marcusfia/JEMA_CSAQS/wiki/images/active_inactive_sensors.jpg

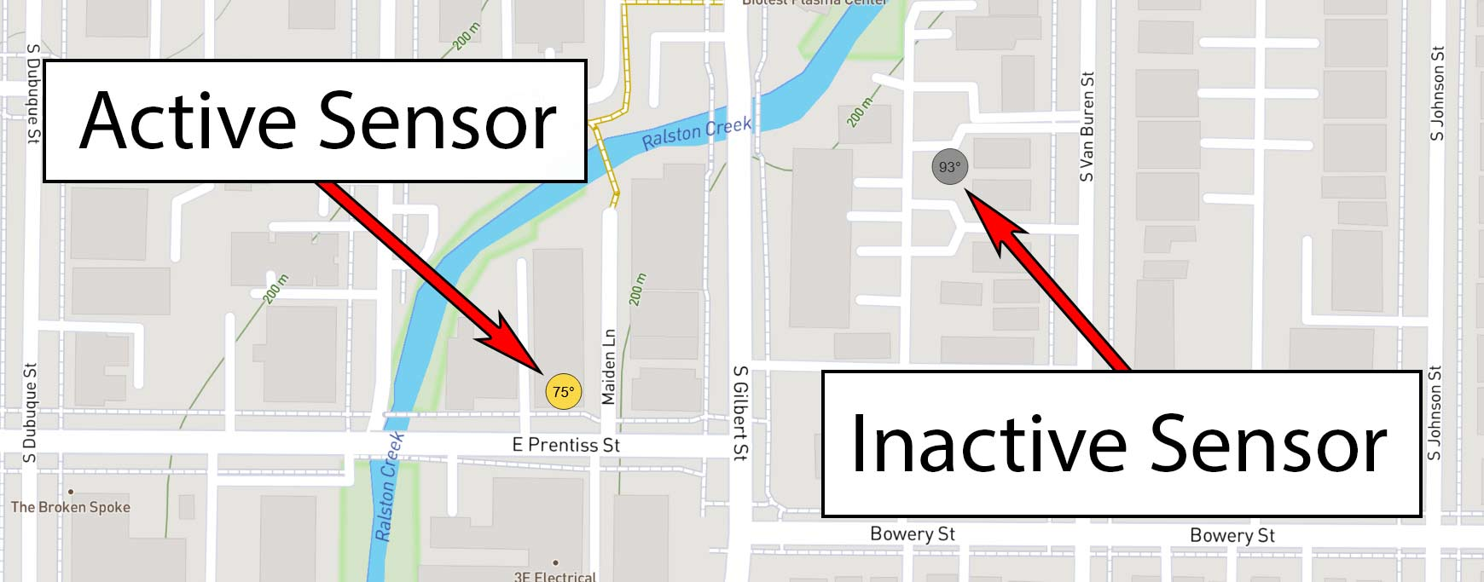
wiki/images/active_inactive_sensors.jpg
