marcusfia/JEMA_CSAQS/wiki/images/antenna.jpg

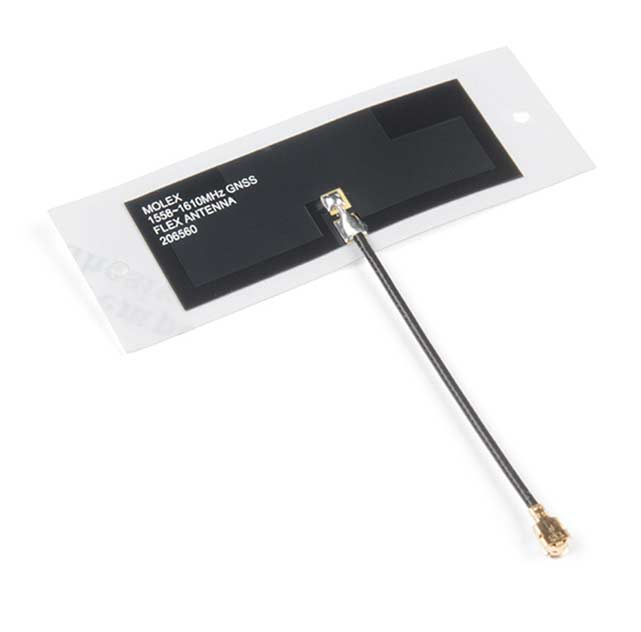
wiki/images/antenna.jpg
