marcusfia/JEMA_CSAQS/wiki/images/batt.jpg

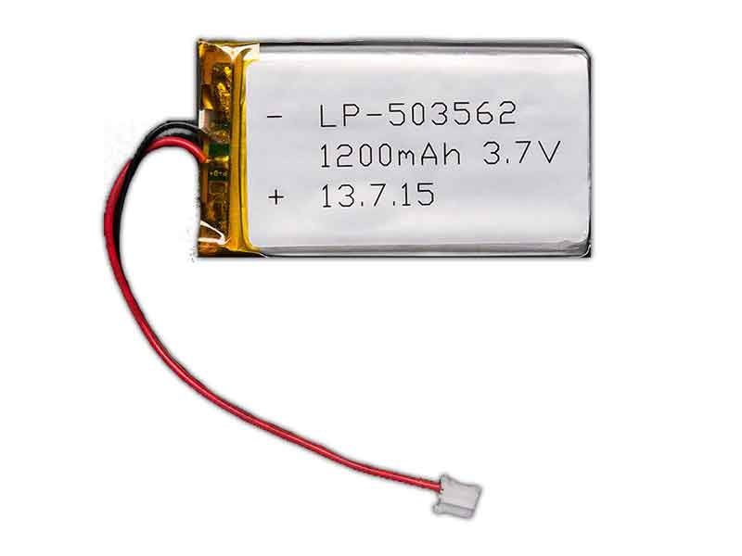
wiki/images/batt.jpg
