marcusfia/JEMA_CSAQS/wiki/images/BME680.jpg

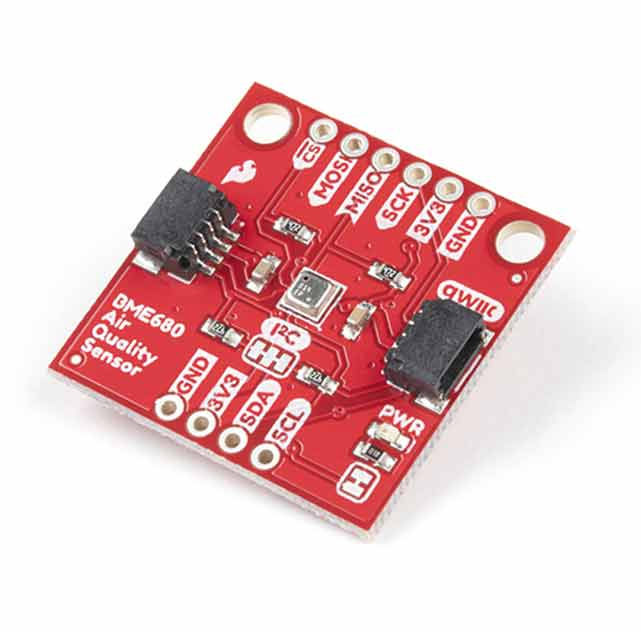
wiki/images/BME680.jpg
