marcusfia/JEMA_CSAQS/wiki/images/cert_3.png

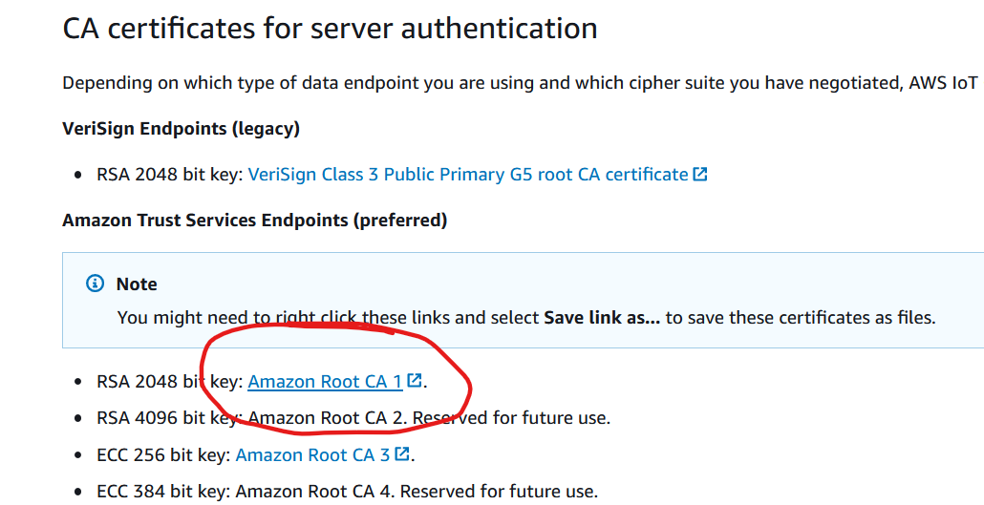
wiki/images/cert_3.png
