marcusfia/JEMA_CSAQS/wiki/images/cert_5.png

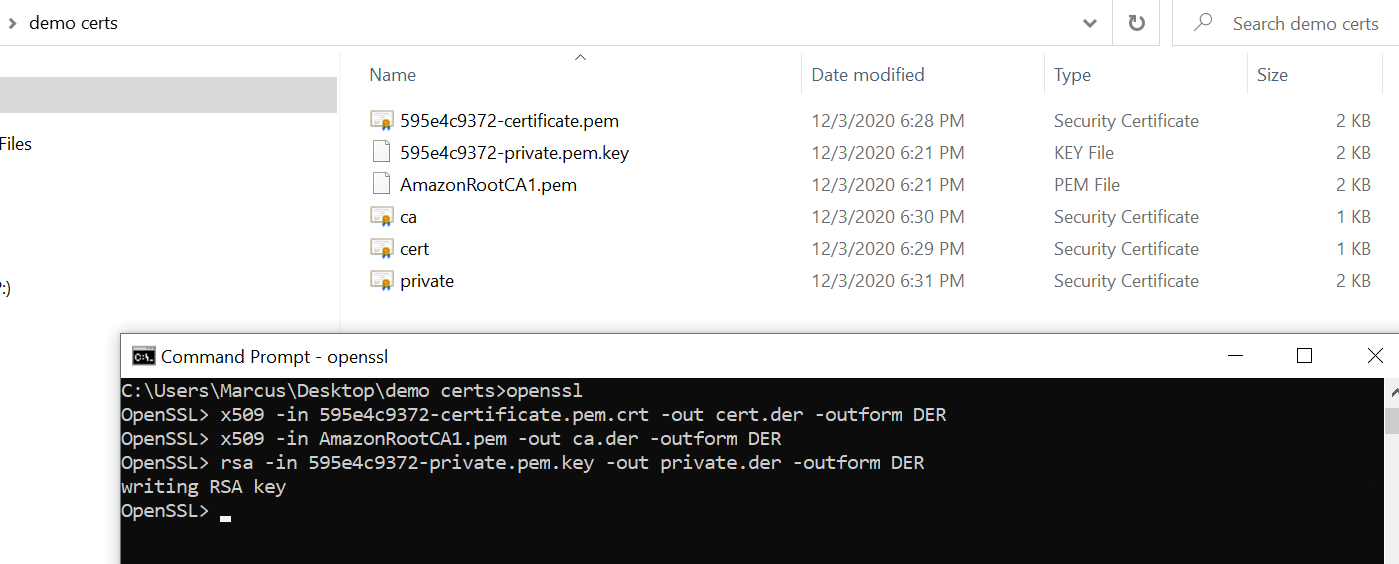
wiki/images/cert_5.png
