marcusfia/JEMA_CSAQS/wiki/images/cert_7.png

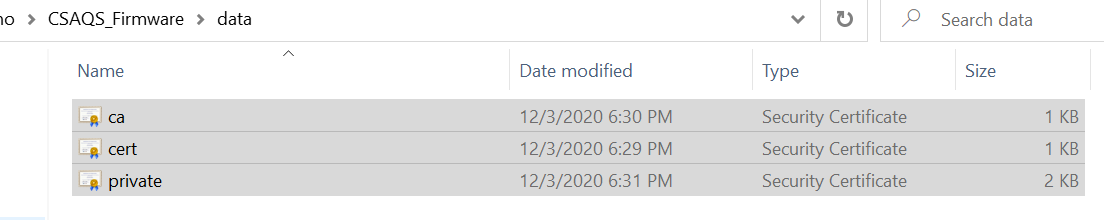
wiki/images/cert_7.png
