marcusfia/JEMA_CSAQS/wiki/images/dataupload.png

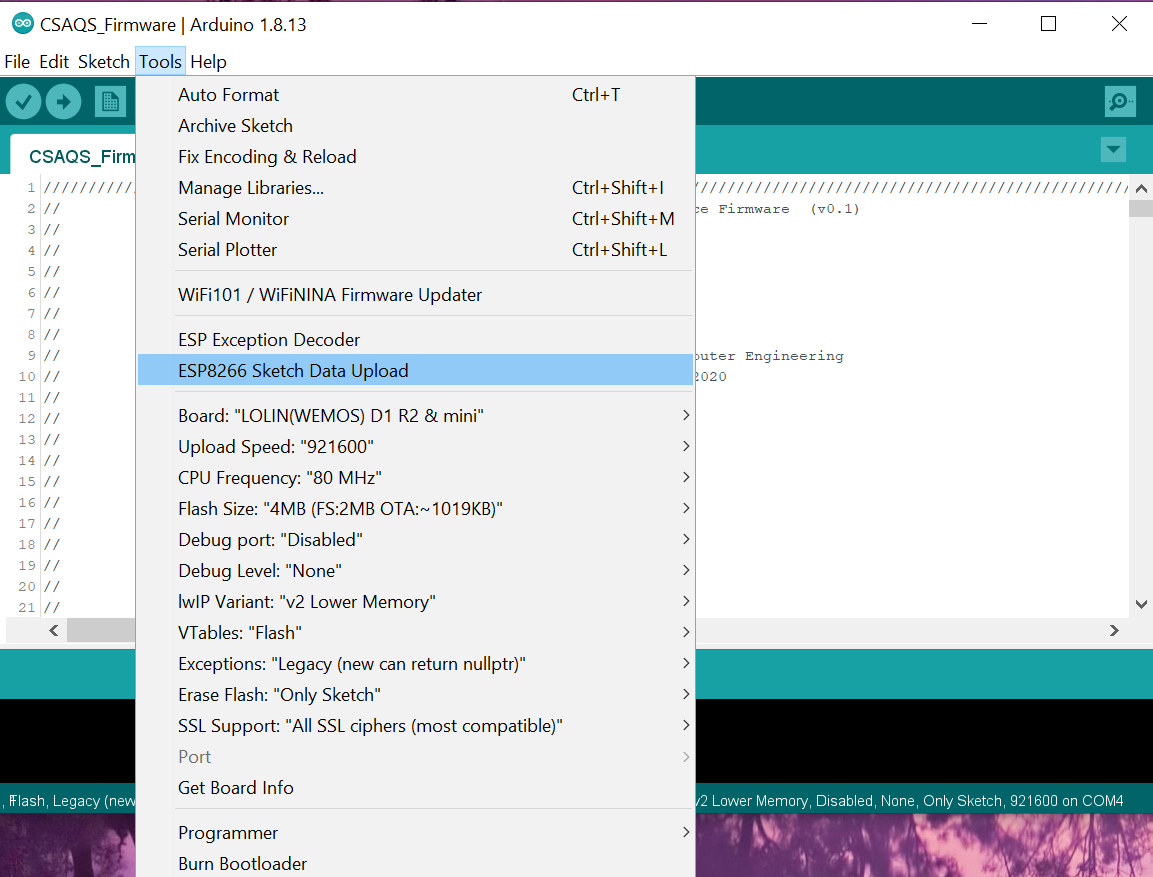
wiki/images/dataupload.png
