marcusfia/JEMA_CSAQS/wiki/images/max30105.jpg

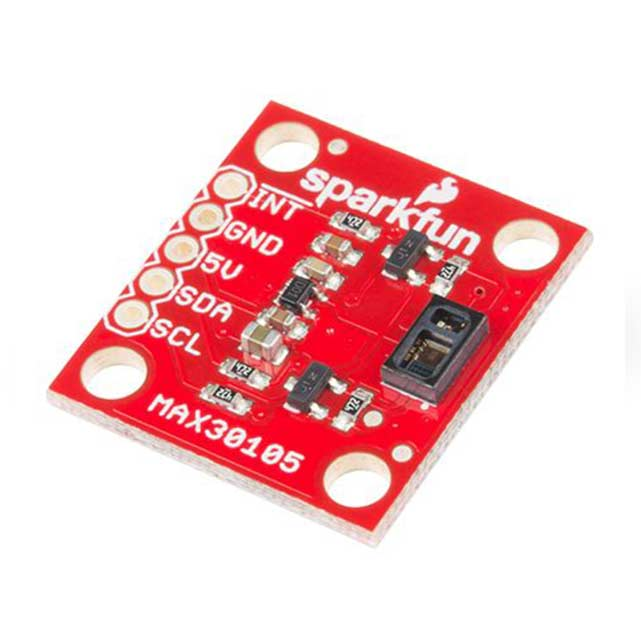
wiki/images/max30105.jpg
