marcusfia/JEMA_CSAQS/wiki/images/mics.jpg

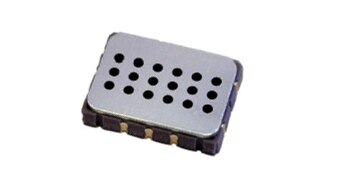
wiki/images/mics.jpg
