marcusfia/JEMA_CSAQS/wiki/images/mobile.jpg

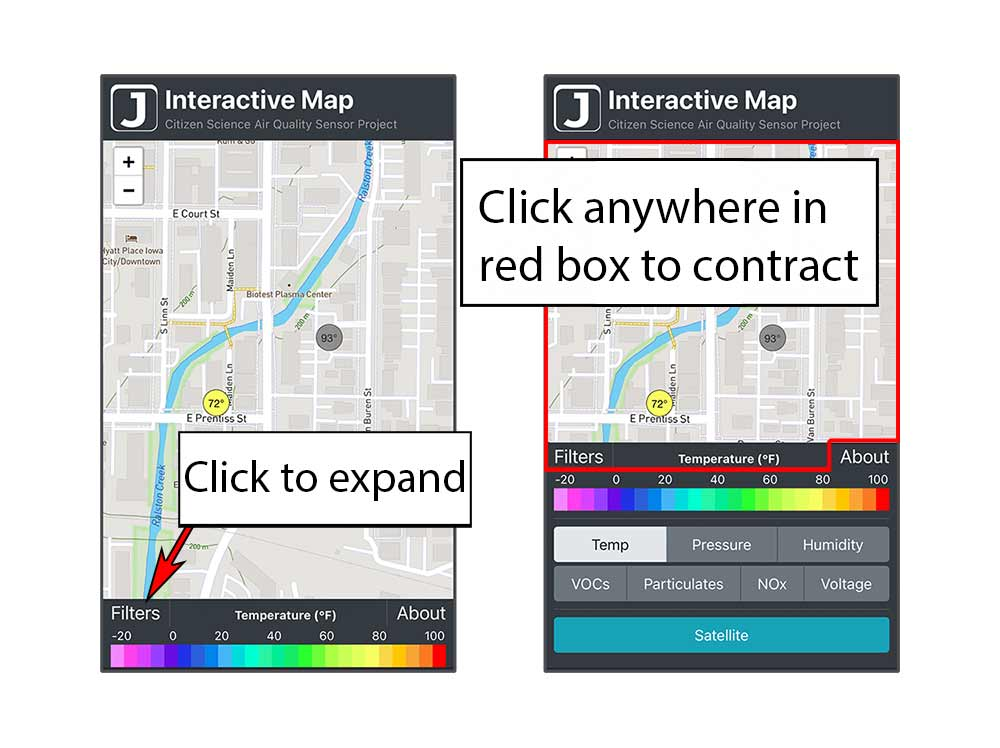
wiki/images/mobile.jpg
