marcusfia/JEMA_CSAQS/wiki/images/NEO-M8U.jpg

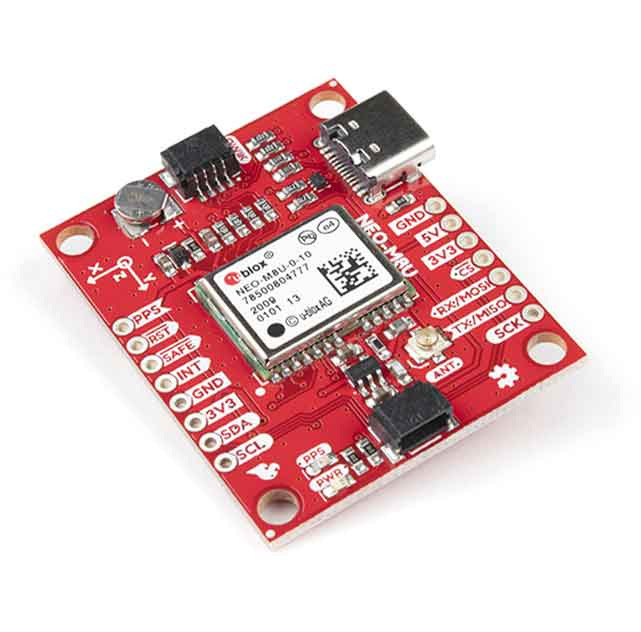
wiki/images/NEO-M8U.jpg
