marcusfia/JEMA_CSAQS/wiki/images/solarpanel.jpg

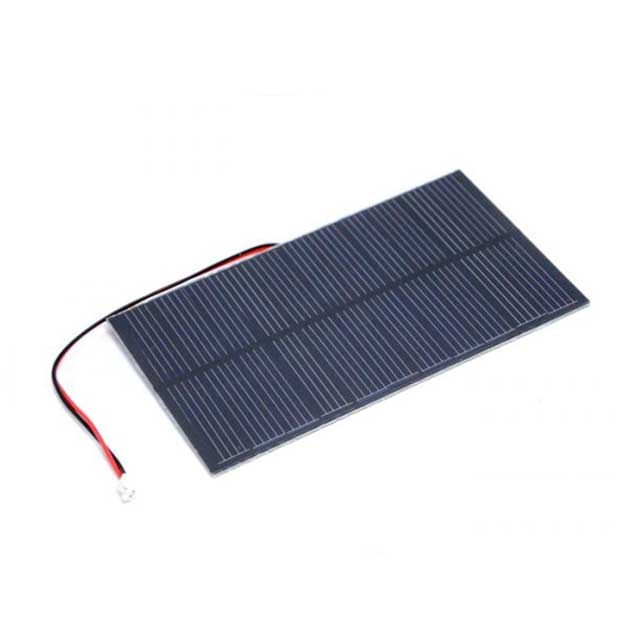
wiki/images/solarpanel.jpg
