marcusfia/JEMA_CSAQS/wiki/images/terrain_map.jpg

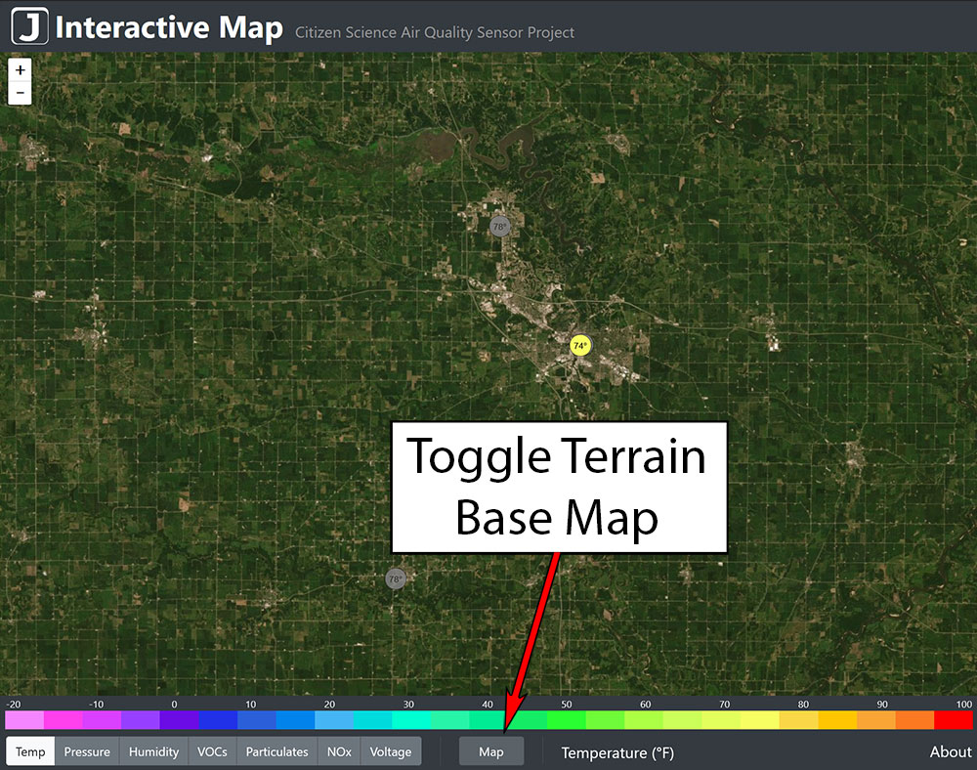
wiki/images/terrain_map.jpg
