marcusfia/JEMA_CSAQS/wiki/images/wemosd1.jpg

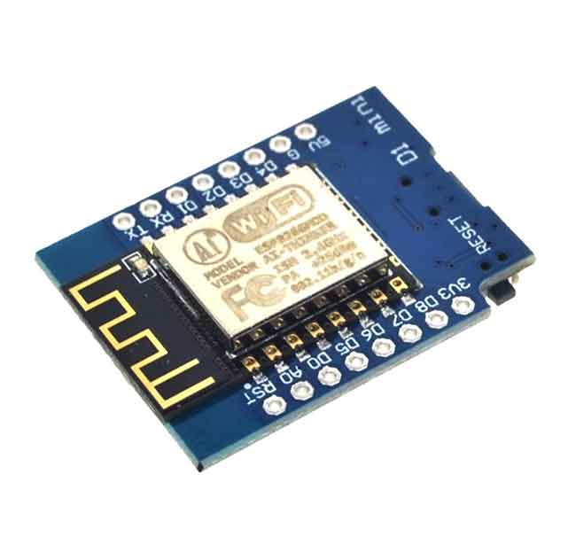
wiki/images/wemosd1.jpg
