marcusfia/JEMA_CSAQS/wiki/images/desktop-data-modal_user_guide.jpg

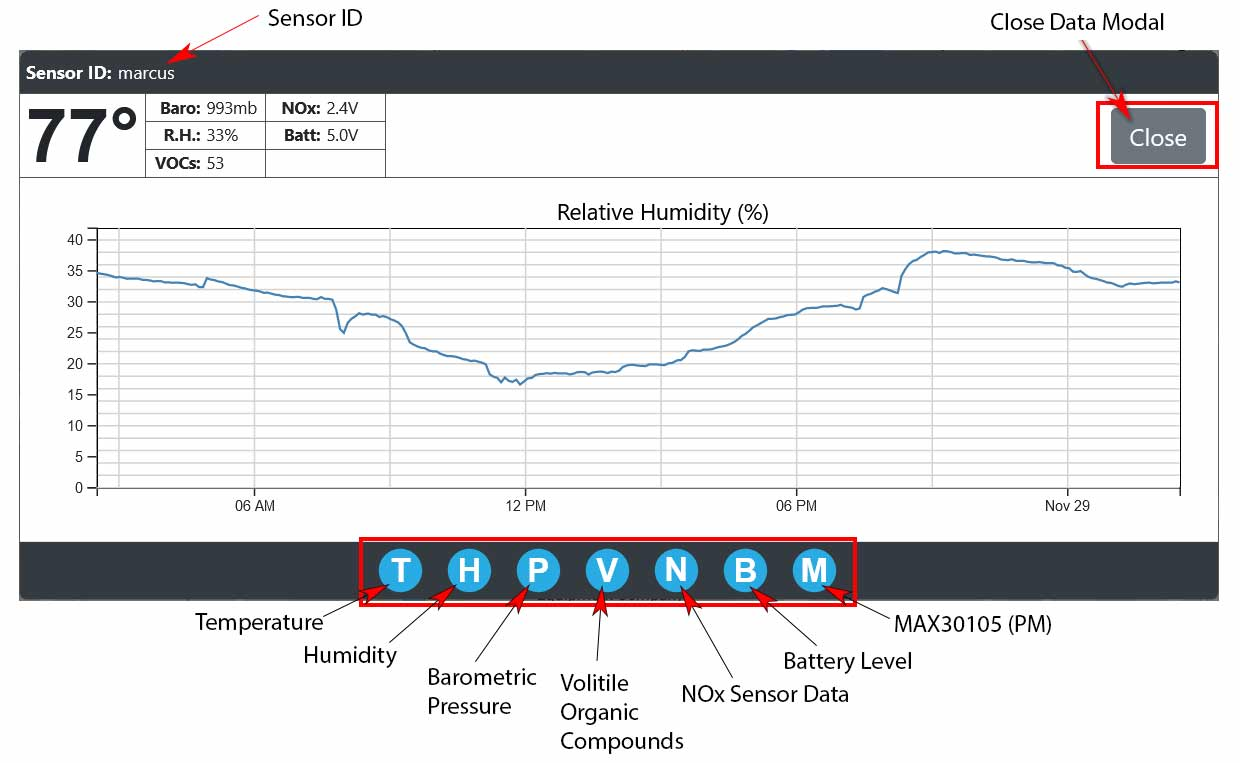
wiki/images/desktop-data-modal_user_guide.jpg
