marcusfia/JEMA_CSAQS/wiki/images/mobile-data-modal_user_guide.jpg

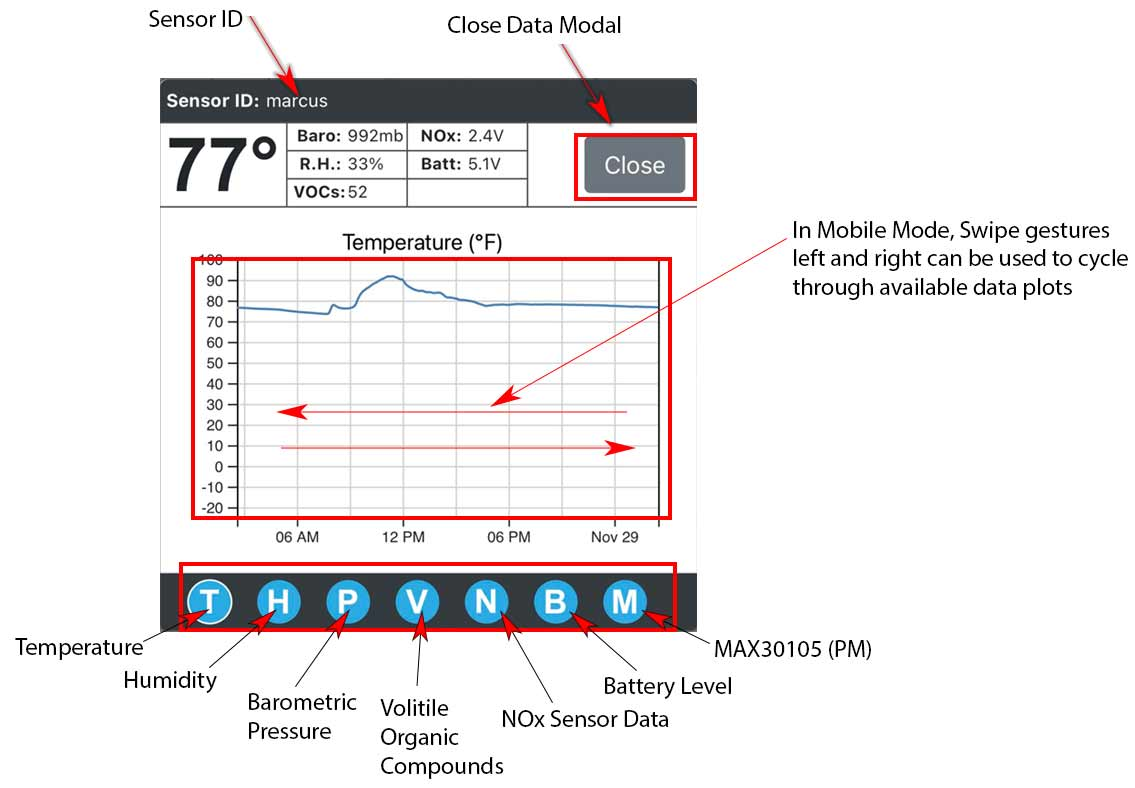
wiki/images/mobile-data-modal_user_guide.jpg
